bhall66/morse-tutor/Cases/N6API/Rectangle/IMAGES/IMG_0502.JPG

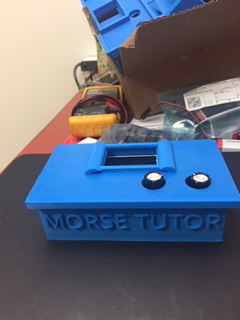
Cases/N6API/Rectangle/IMAGES/IMG_0502.JPG
