bhall66/morse-tutor/Cases/N6API/Rectangle/IMAGES/IMG_0505.JPG

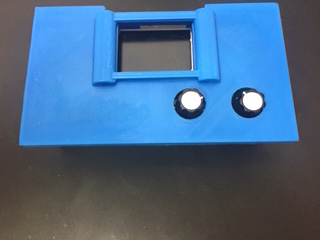
Cases/N6API/Rectangle/IMAGES/IMG_0505.JPG
