bhall66/morse-tutor/Cases/N6API/Rectangle/IMAGES/IMG_0512.JPG

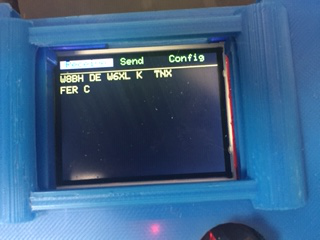
Cases/N6API/Rectangle/IMAGES/IMG_0512.JPG
