bhall66/morse-tutor/Cases/N6API/Square/IMAGES/IMG_0462.JPG

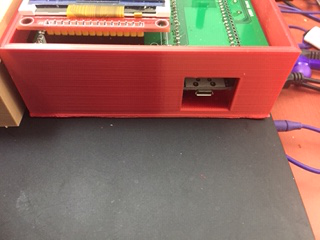
Cases/N6API/Square/IMAGES/IMG_0462.JPG
