bhall66/morse-tutor/Cases/N6API/Square/IMAGES/IMG_0466.JPG

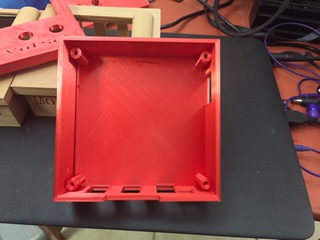
Cases/N6API/Square/IMAGES/IMG_0466.JPG
