bhall66/morse-tutor/Cases/N6API/Square/IMAGES/IMG_0523.JPG

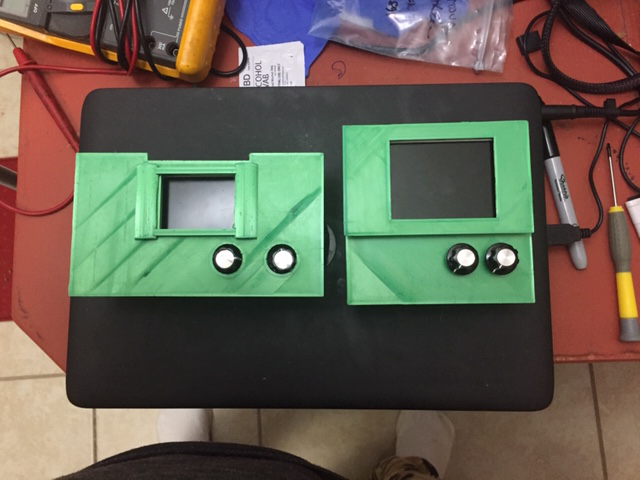
Cases/N6API/Square/IMAGES/IMG_0523.JPG
