bhall66/morse-tutor/Cases/WJ6U/Images/IMG_0741.JPG

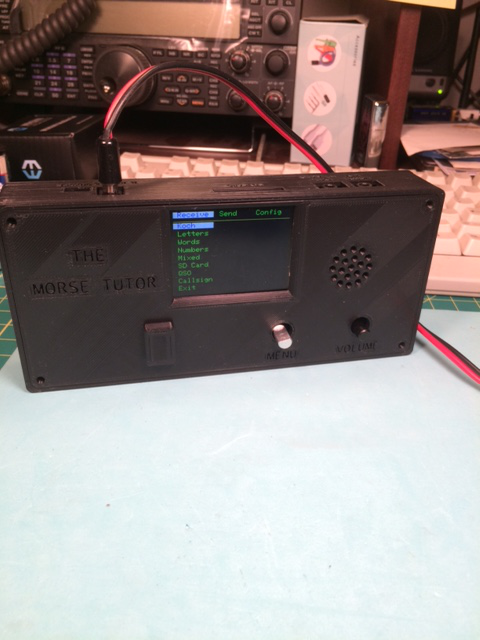
Cases/WJ6U/Images/IMG_0741.JPG
