bhall66/morse-tutor/Cases/WJ6U/Images/IMG_0742.JPG

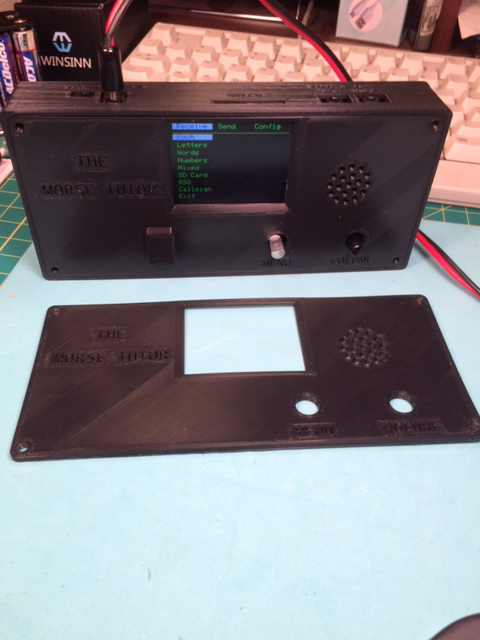
Cases/WJ6U/Images/IMG_0742.JPG
