bhall66/morse-tutor/Cases/WJ6U/Images/IMG_0743.JPG

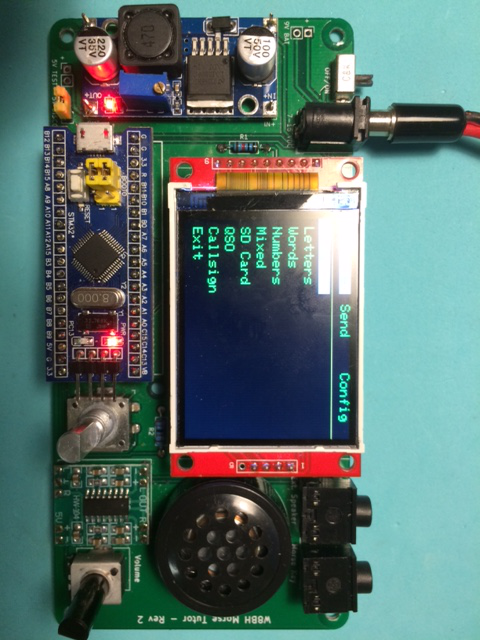
Cases/WJ6U/Images/IMG_0743.JPG
