bhall66/morse-tutor/MorseTutor_ESP32/PCB/rev 1/3D layout - ESP32.JPG

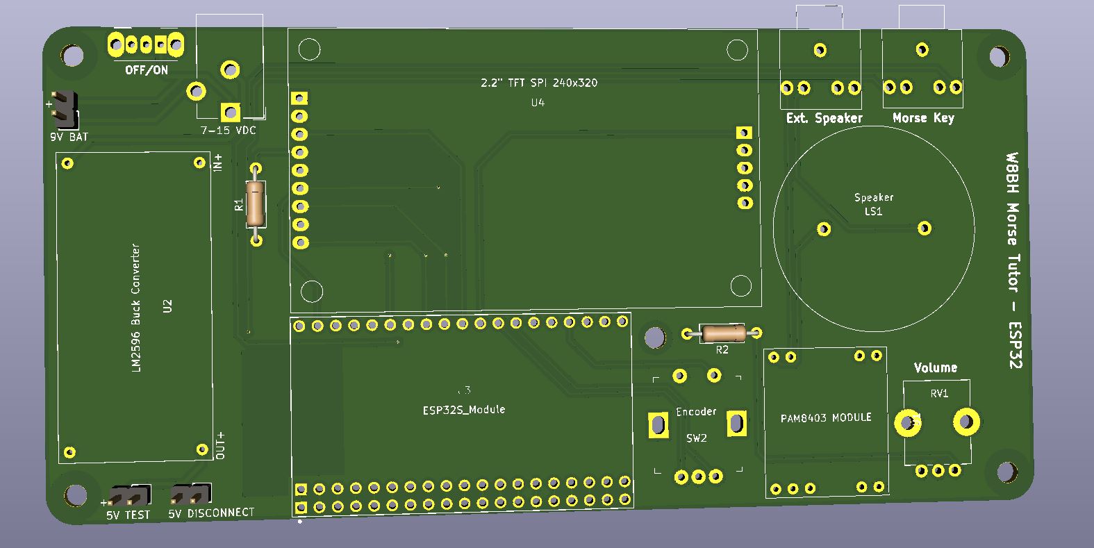
MorseTutor_ESP32/PCB/rev 1/3D layout - ESP32.JPG
