bhall66/morse-tutor/MorseTutor_ESP32/PCB/rev 2B/MorseTutorESP32_rev2B_back.JPG

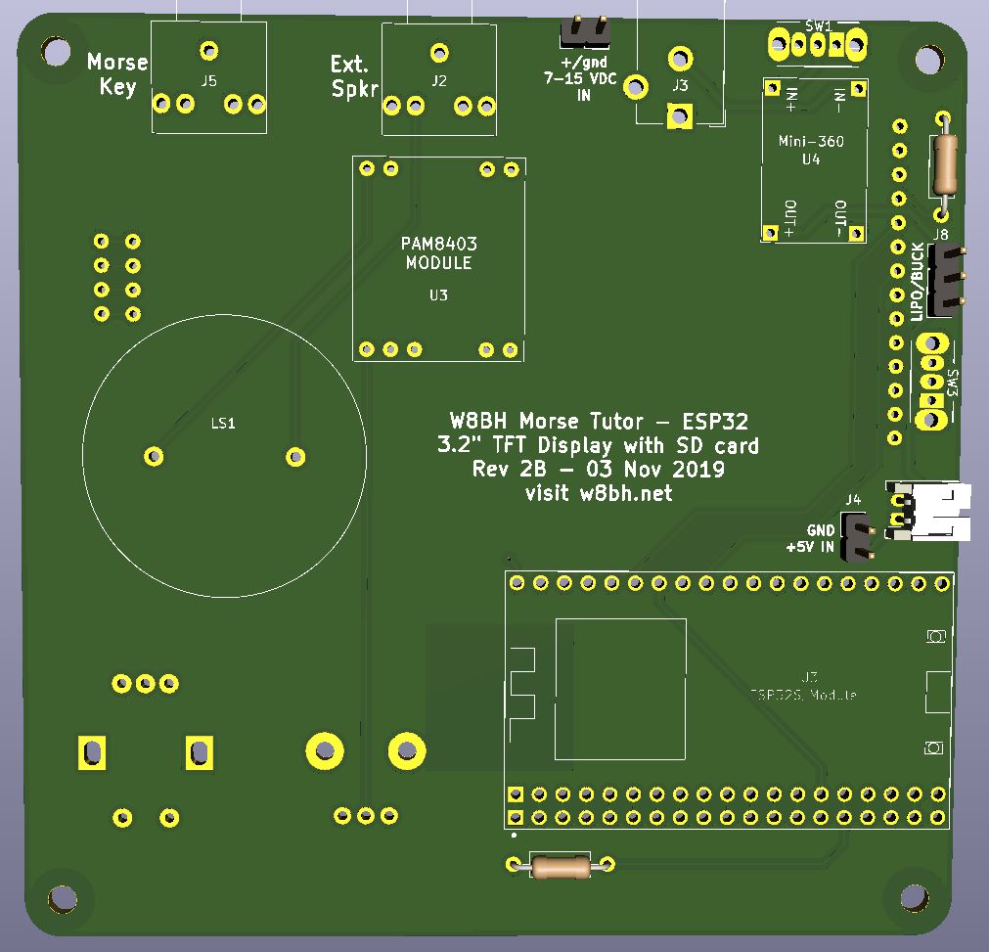
MorseTutor_ESP32/PCB/rev 2B/MorseTutorESP32_rev2B_back.JPG
