bhall66/morse-tutor/PCB/3D layout.jpg

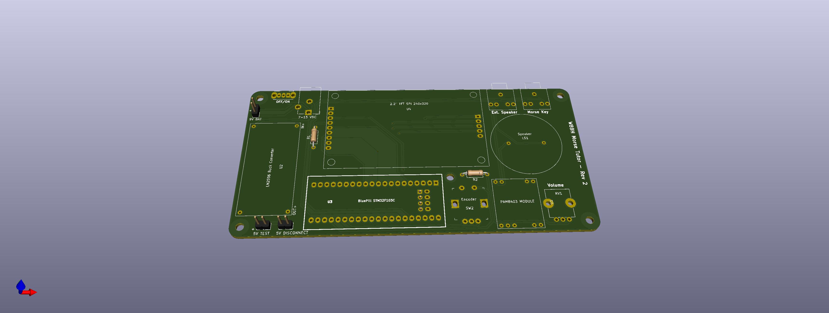
PCB/3D layout.jpg
